nstrappazzonc/keyboard/assets/KeyboardV1.0Back.png

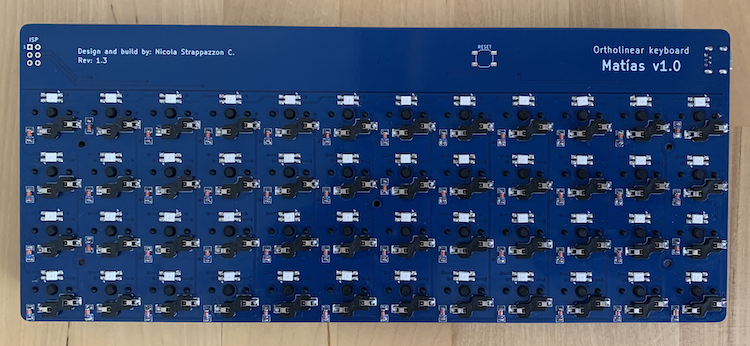
assets/KeyboardV1.0Back.png
