nstrappazzonc/keyboard/assets/KeyboardV1.0Protoboard.png

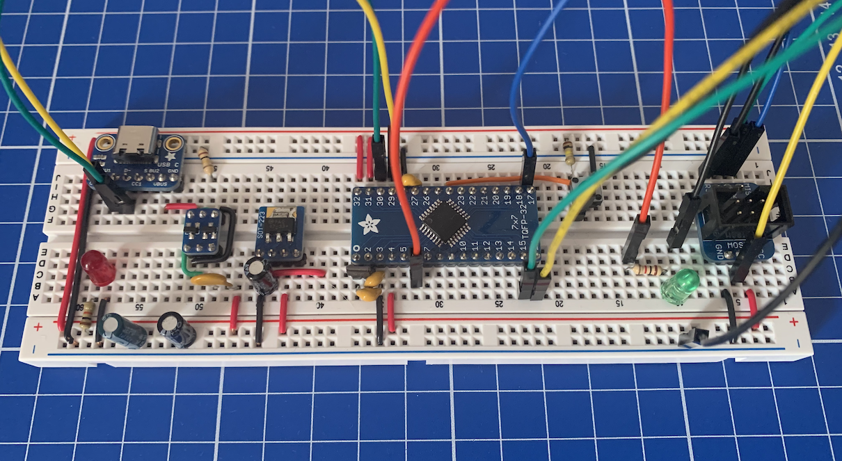
assets/KeyboardV1.0Protoboard.png
