nstrappazzonc/keyboard/assets/KeyboardV1.0VS.png

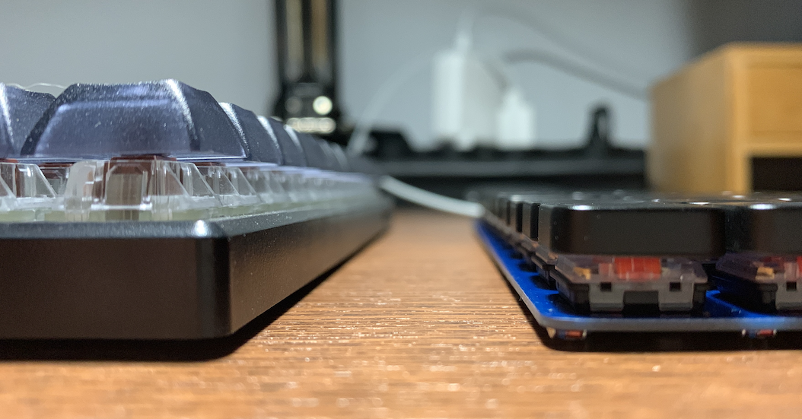
assets/KeyboardV1.0VS.png
