nstrappazzonc/keyboard/assets/MatiasV1Front.png

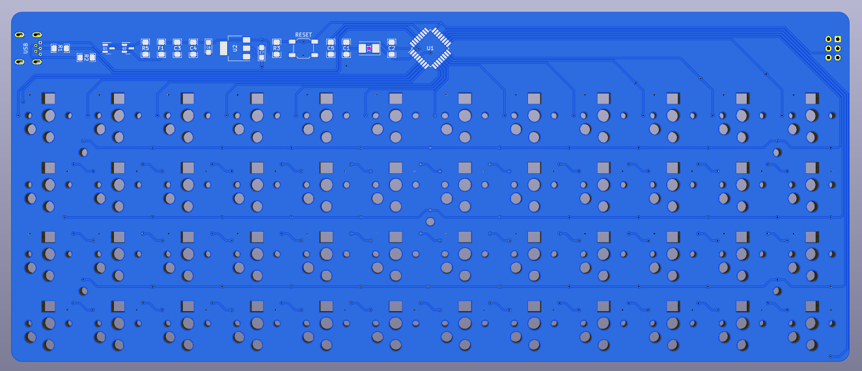
assets/MatiasV1Front.png
