nstrappazzonc/keyboard/assets/USBMiniB01.png

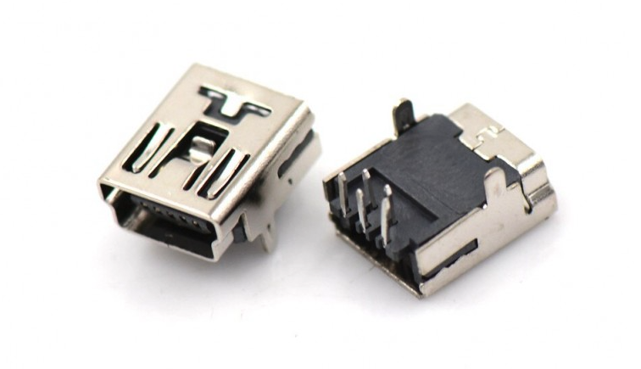
assets/USBMiniB01.png
