nstrappazzonc/keyboard/assets/USBMiniB02.png

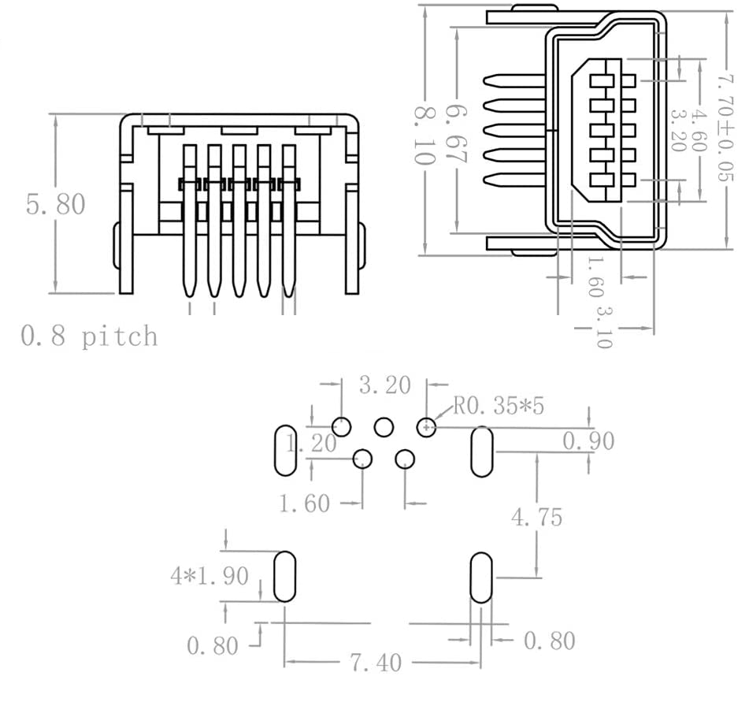
assets/USBMiniB02.png
