nstrappazzonc/keyboard/assets/USBMiniB03.png

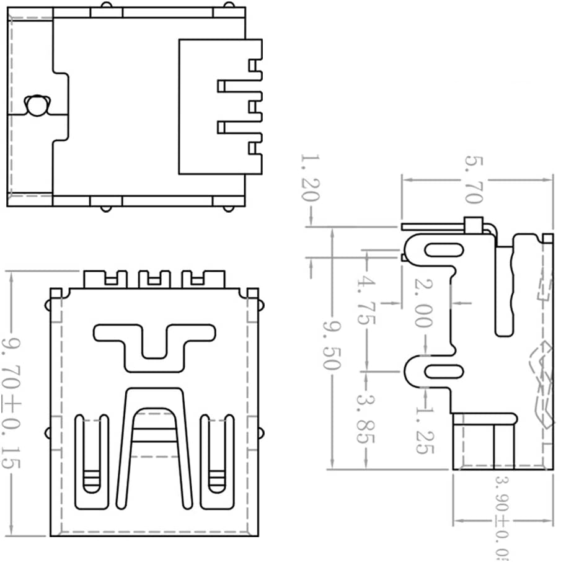
assets/USBMiniB03.png
