nstrappazzonc/keyboard/assets/KeyboardV1.0Test02.png

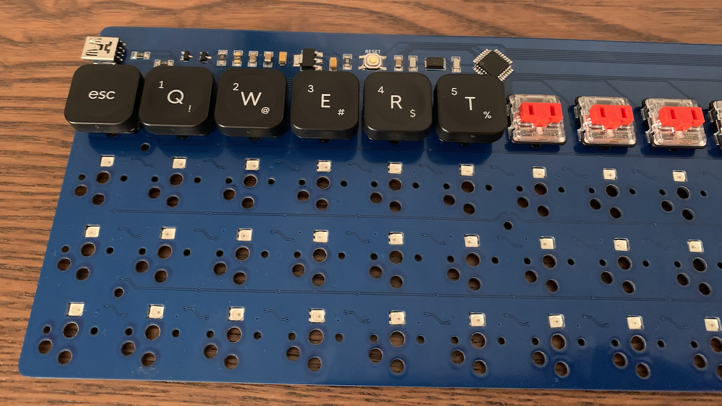
assets/KeyboardV1.0Test02.png
