nstrappazzonc/keyboard/assets/KeyboardV1.0Test.png

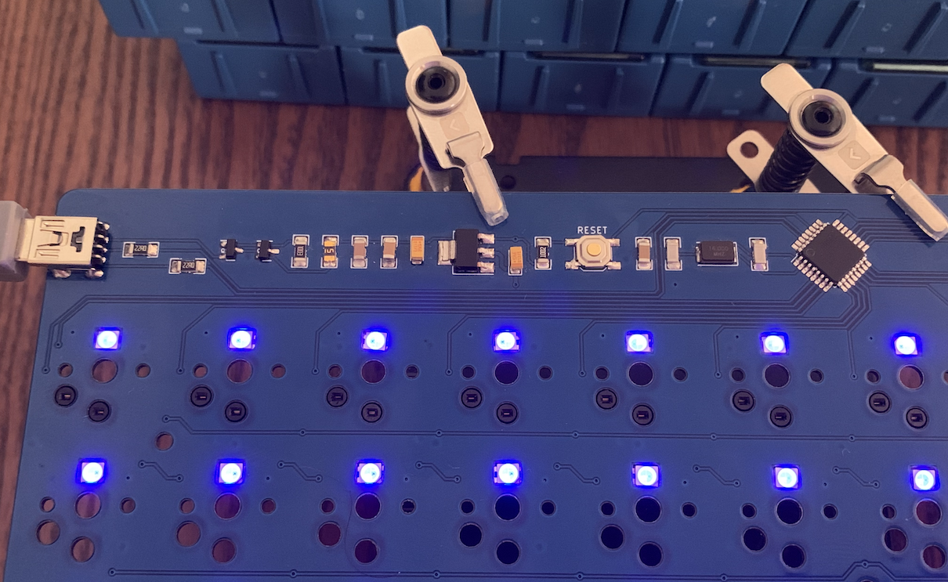
assets/KeyboardV1.0Test.png
